clemarfolly/Microdigital-TK2000/EsquemaOriginal/tk2000.jpg

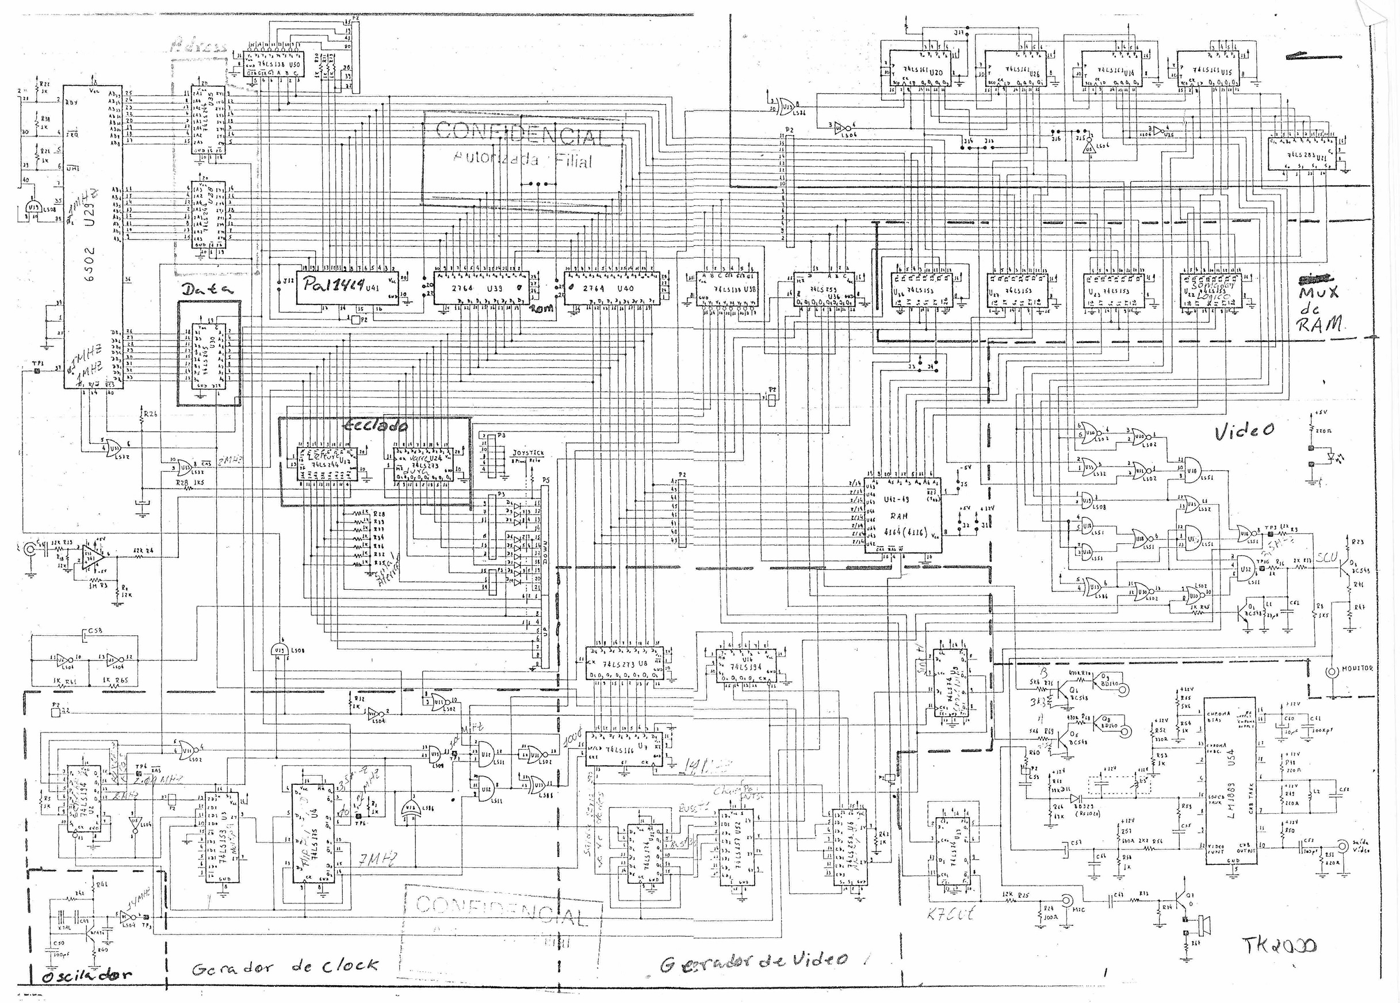
EsquemaOriginal/tk2000.jpg
