clemarfolly/Microdigital-TK2000/Fotos/Corrigido/tk2000_b.jpg

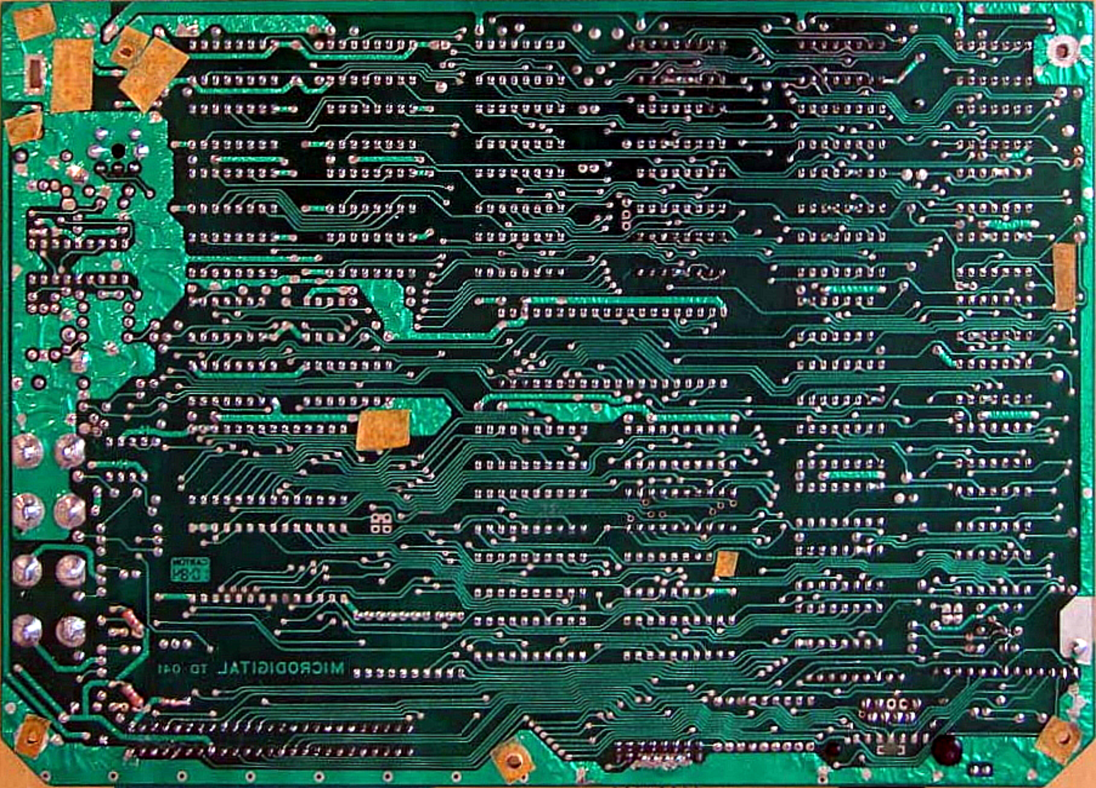
Fotos/Corrigido/tk2000_b.jpg
