clemarfolly/Microdigital-TK2000/Fotos/Corrigido/tk2000_pre_b.png

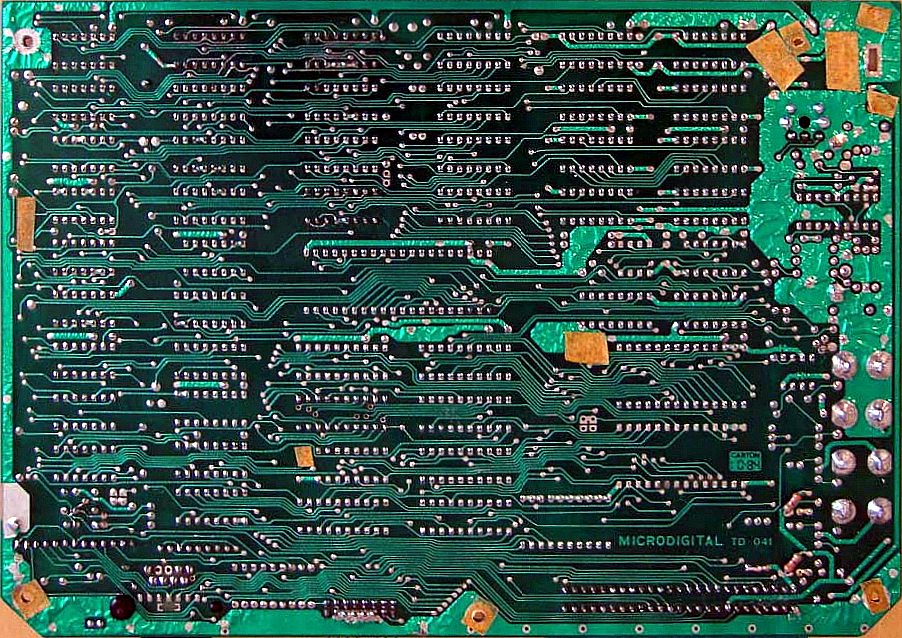
Fotos/Corrigido/tk2000_pre_b.png
