clemarfolly/Microdigital-TK2000/Fotos/Corrigido/tk2000_pre_f2.jpg

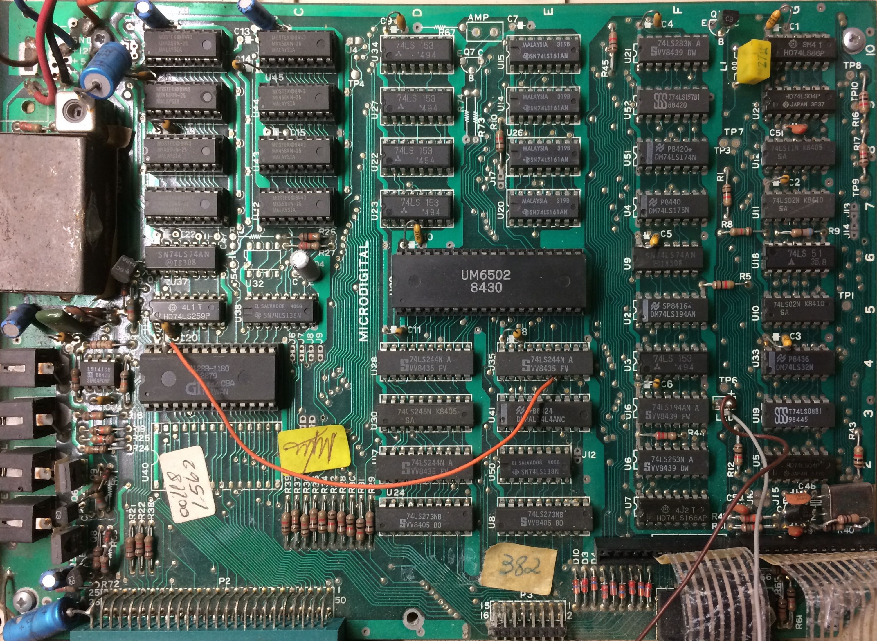
Fotos/Corrigido/tk2000_pre_f2.jpg
