clemarfolly/Microdigital-TK2000/Fotos/Corrigido/tk2000_pre_f.jpg

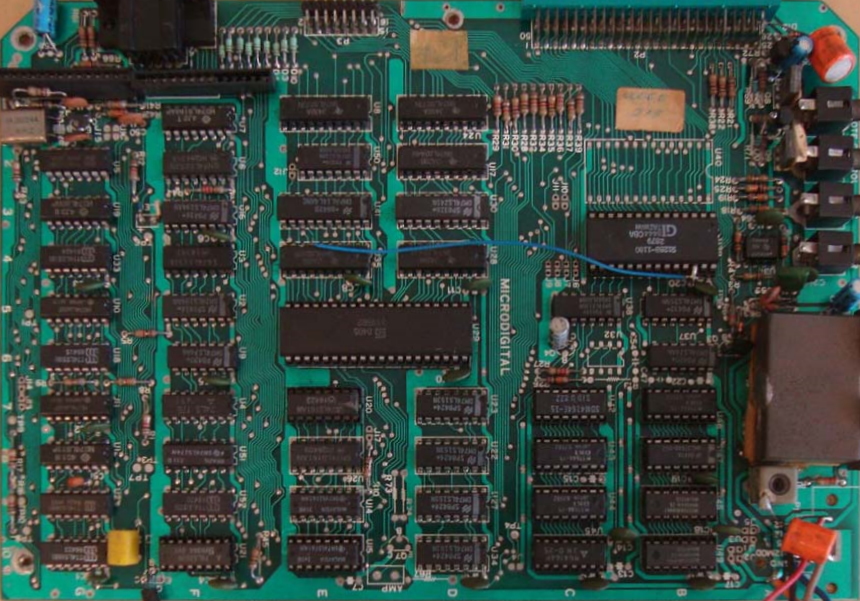
Fotos/Corrigido/tk2000_pre_f.jpg
