clemarfolly/Microdigital-TK2000/Fotos/Original/9.jpg

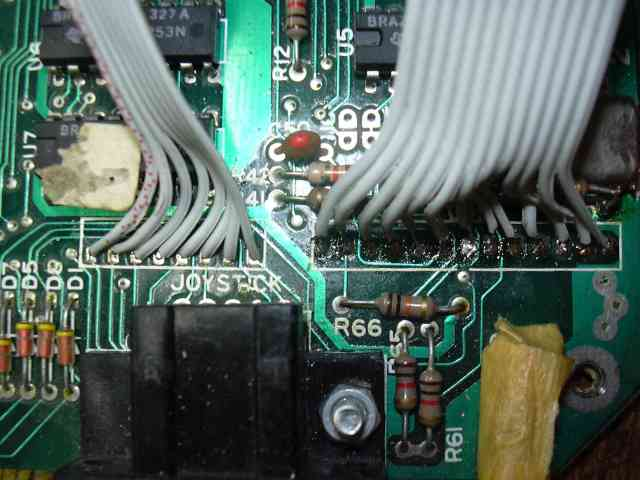
Fotos/Original/9.jpg
