clemarfolly/Microdigital-TK2000/Fotos/Original/117225193_1675733515915561_8471204110769268114_n.jpg

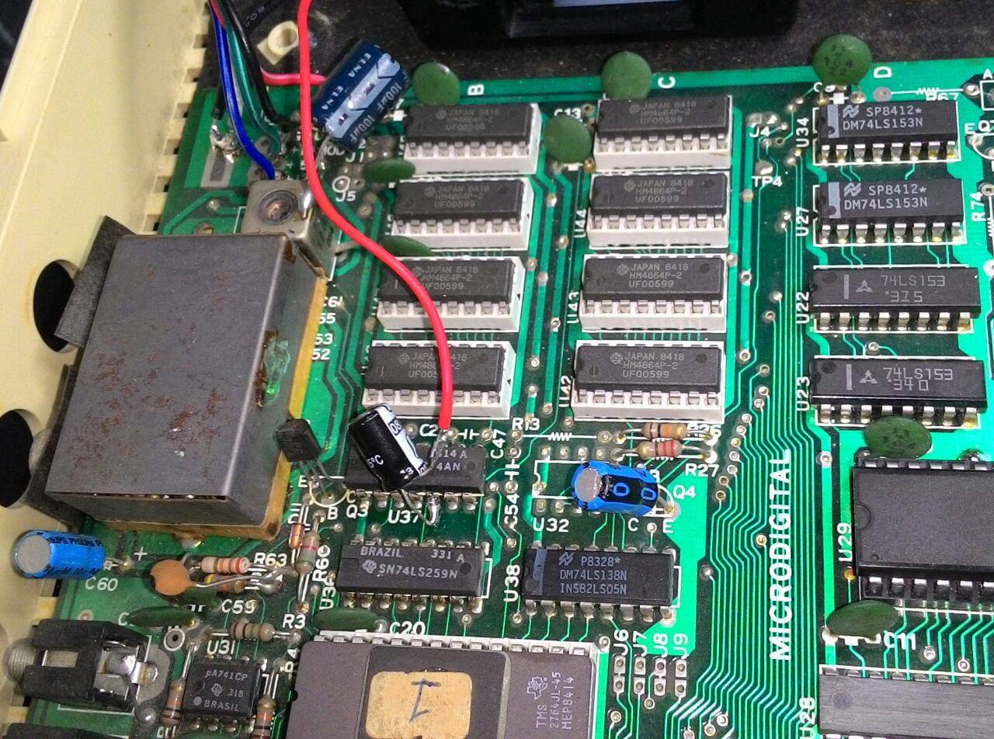
Fotos/Original/117225193_1675733515915561_8471204110769268114_n.jpg
