clemarfolly/Microdigital-TK2000/Fotos/Original/fotospcbtk20002/20221020_185743.jpg

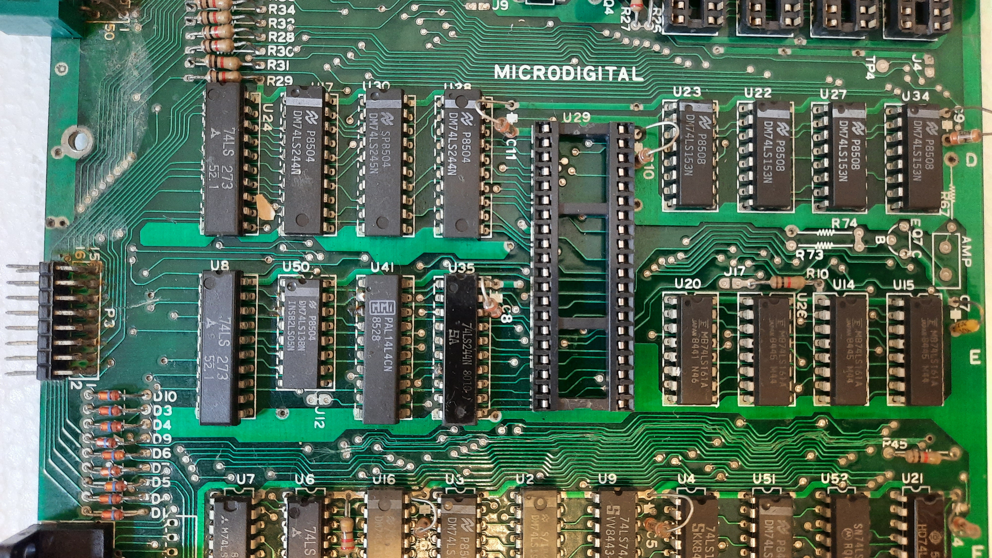
Fotos/Original/fotospcbtk20002/20221020_185743.jpg
