clemarfolly/Microdigital-TK2000/Fotos/Original/Multitech_MPF-II_02.jpg

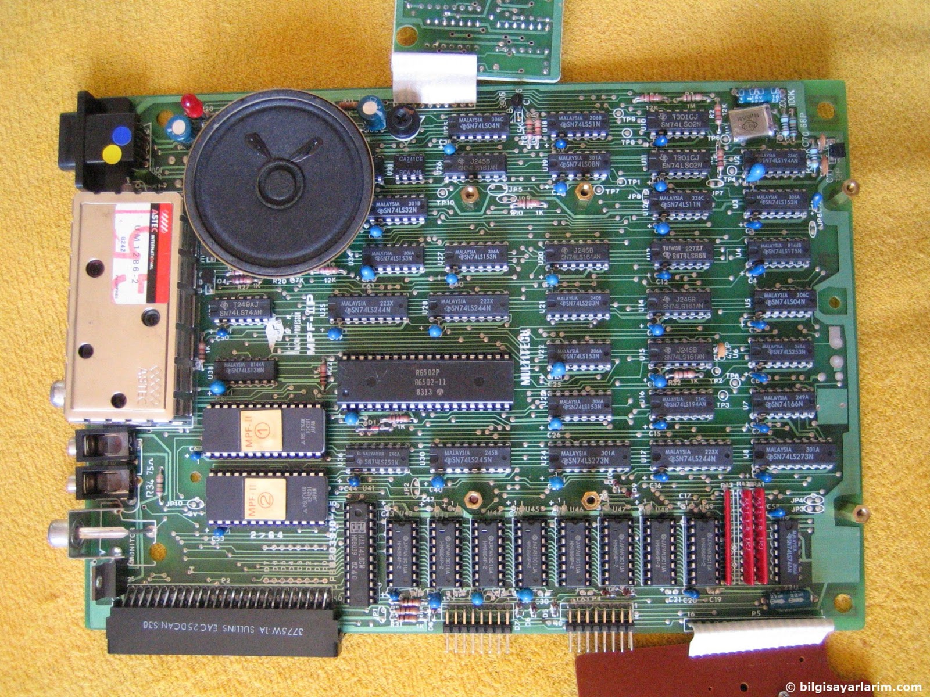
Fotos/Original/Multitech_MPF-II_02.jpg
