clemarfolly/Microdigital-TK2000/Fotos/Original/Projetos_TK2000_clareamento(9).jpg

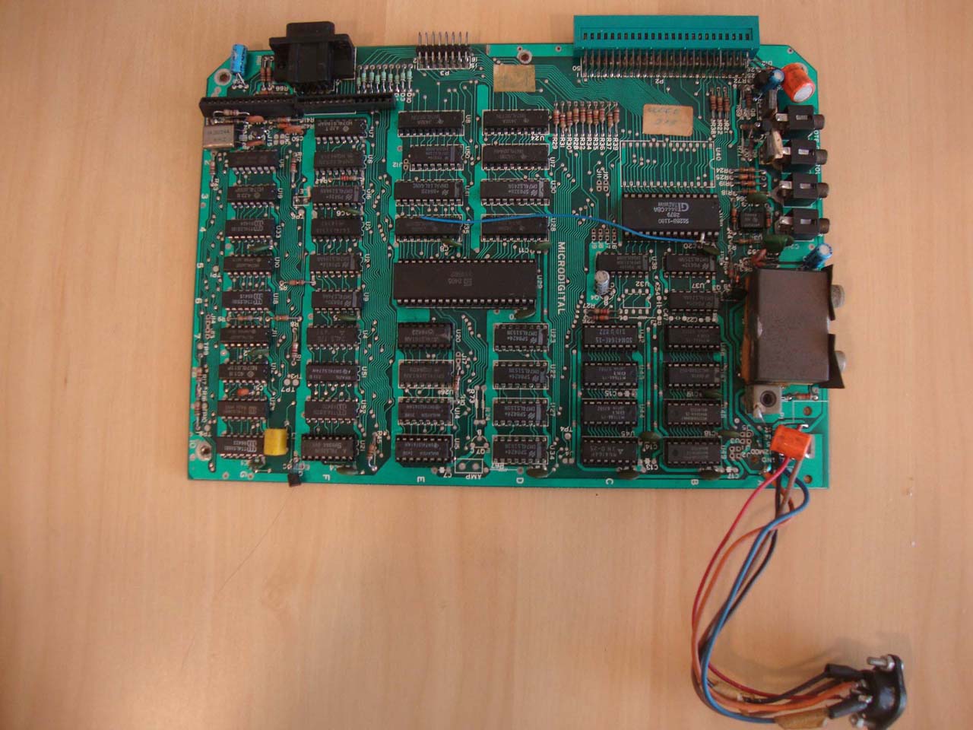
Fotos/Original/Projetos_TK2000_clareamento(9).jpg
