clemarfolly/Microdigital-TK2000/Fotos/Original/Projetos_TK2000_saida_som(3).jpg

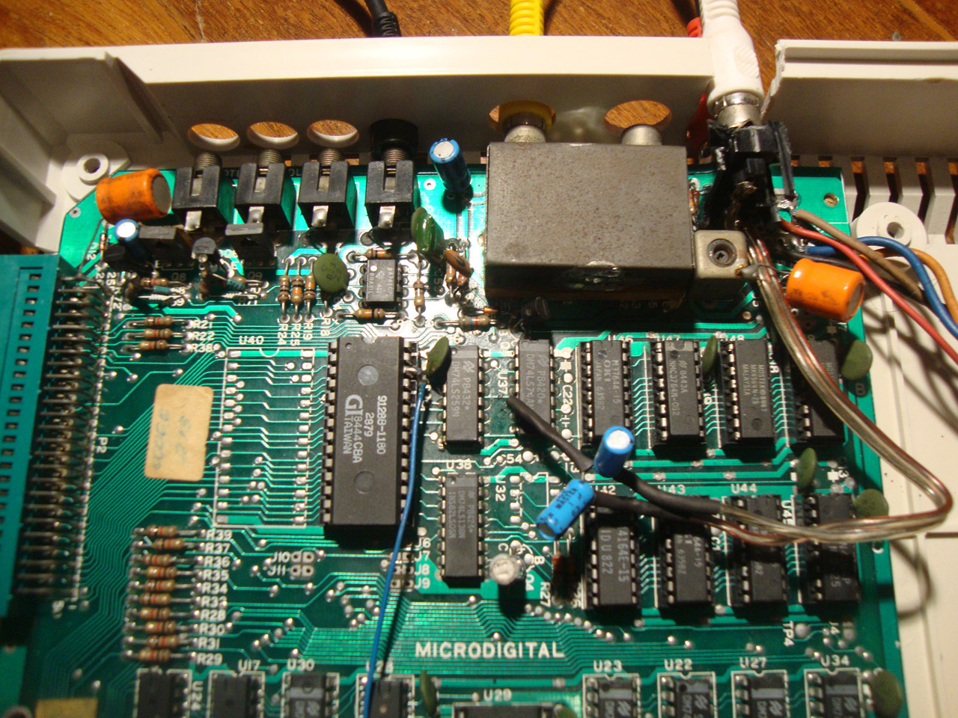
Fotos/Original/Projetos_TK2000_saida_som(3).jpg
