clemarfolly/Microdigital-TK2000/Fotos/Original/tk-2000 (5).jpg

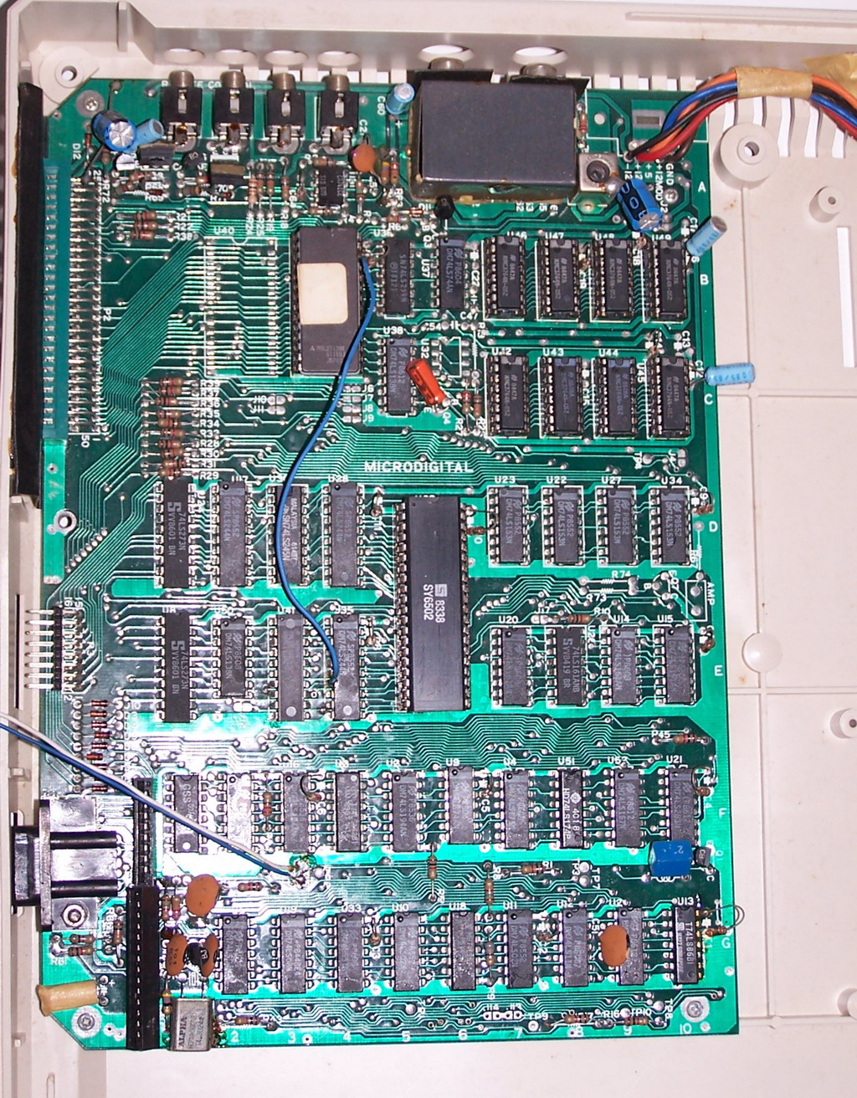
Fotos/Original/tk-2000 (5).jpg
