clemarfolly/Microdigital-TK2000/Imagens/tk2000.png

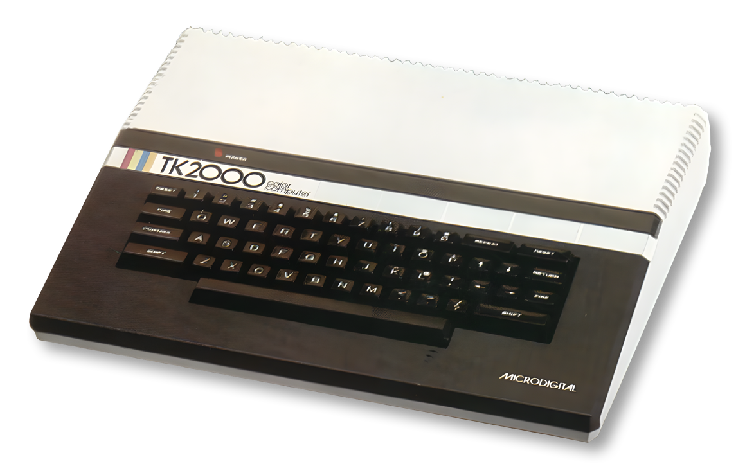
Imagens/tk2000.png
