clemarfolly/Microdigital-TK2000/Imagens/TK2000_b.png

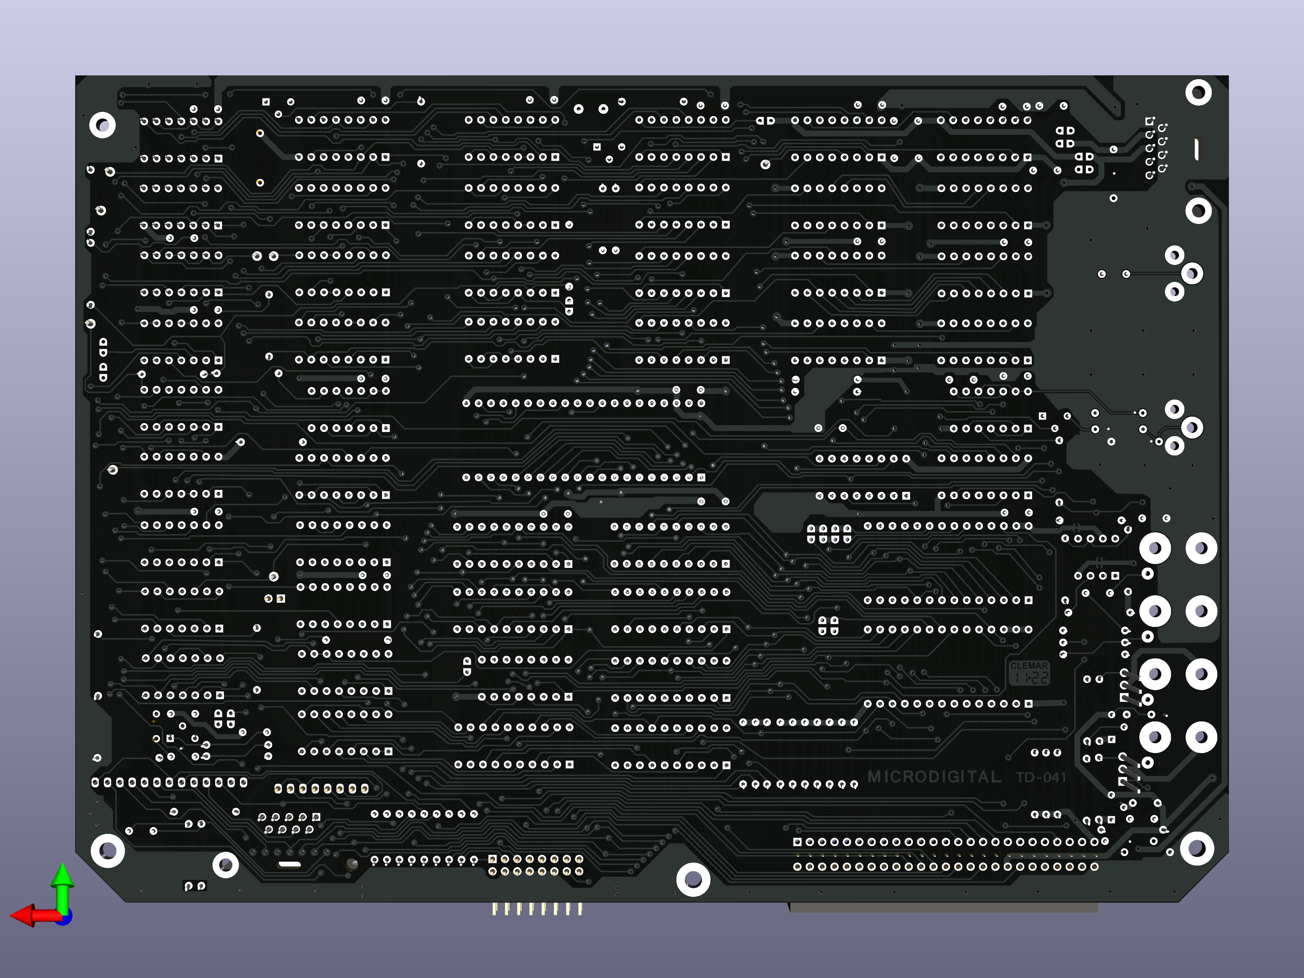
Imagens/TK2000_b.png
