clemarfolly/Microdigital-TK2000/Imagens/TK2000_b_comparacao.PNG

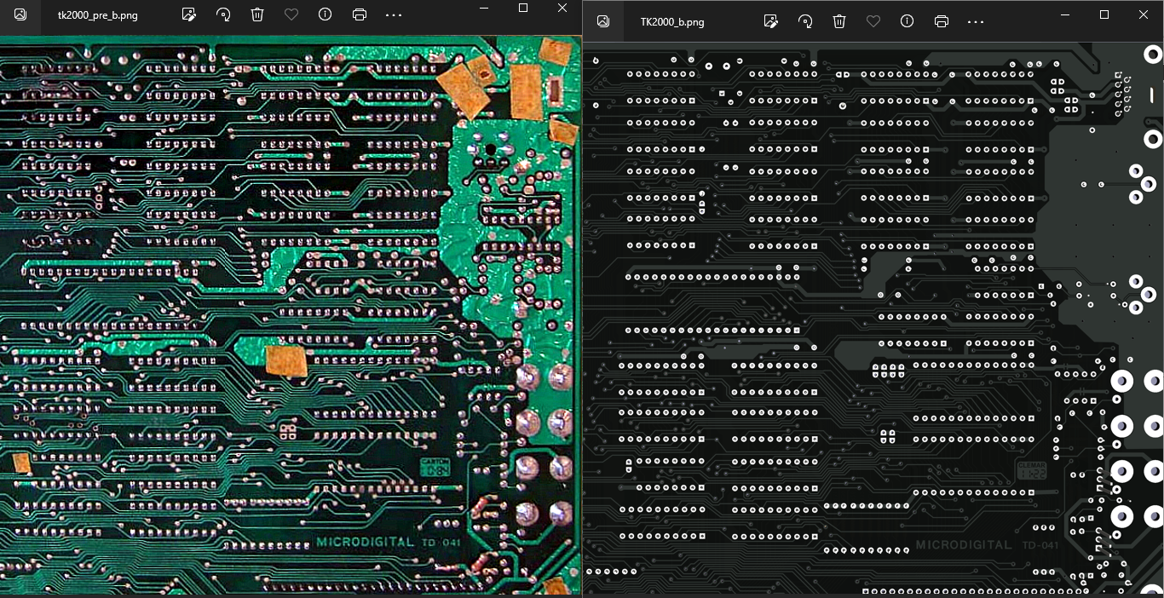
Imagens/TK2000_b_comparacao.PNG
