clemarfolly/Microdigital-TK2000/Imagens/TK2000_f_comparacao.PNG

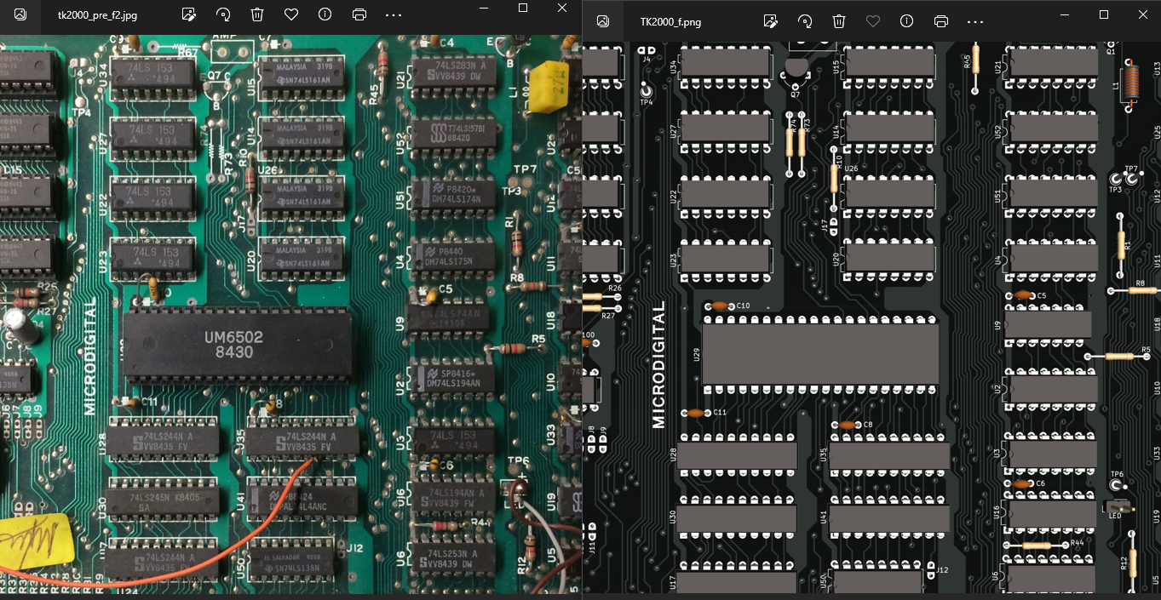
Imagens/TK2000_f_comparacao.PNG
