clemarfolly/Microdigital-TK2000/Imagens/tk2000_roteamento.png

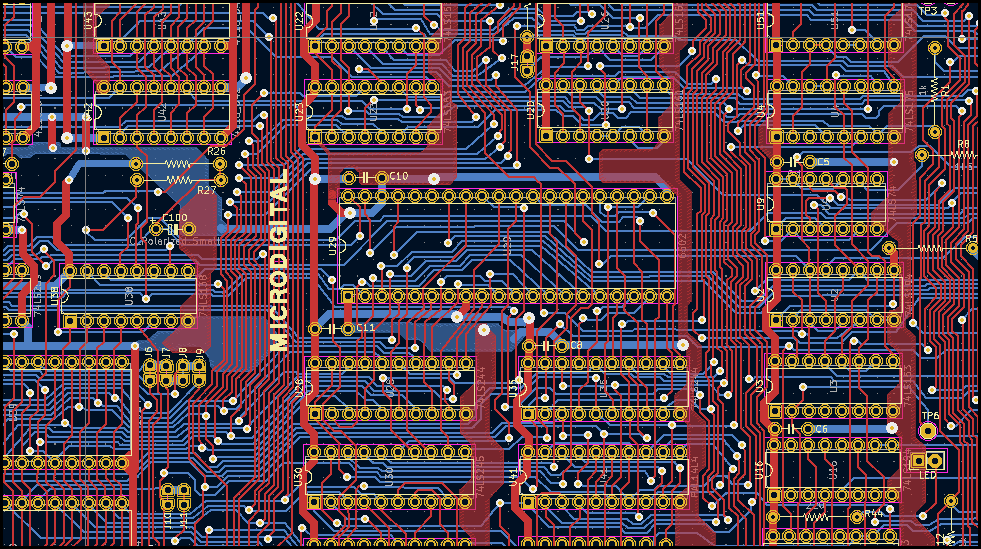
Imagens/tk2000_roteamento.png
