clemarfolly/Microdigital-TK2000/Interface de Drive/Fotos/placa_drive_lc_cheia.jpg

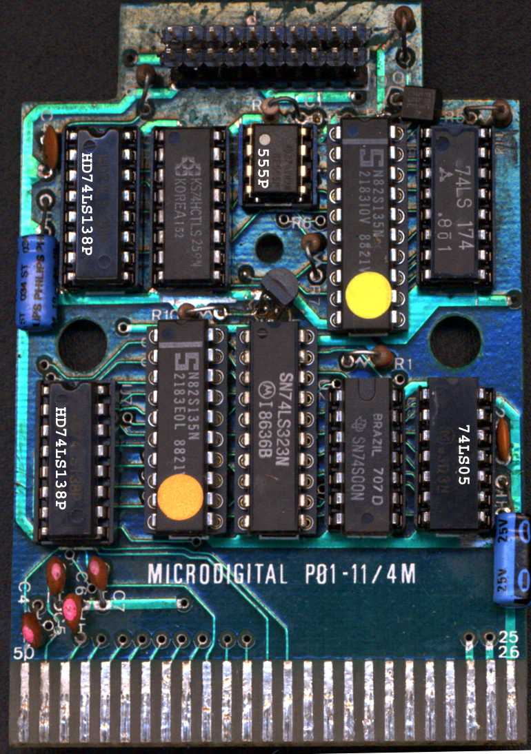
Interface de Drive/Fotos/placa_drive_lc_cheia.jpg
