clemarfolly/Microdigital-TK2000/Interface de Drive/Fotos/placa_drive_ls_cheia.jpg

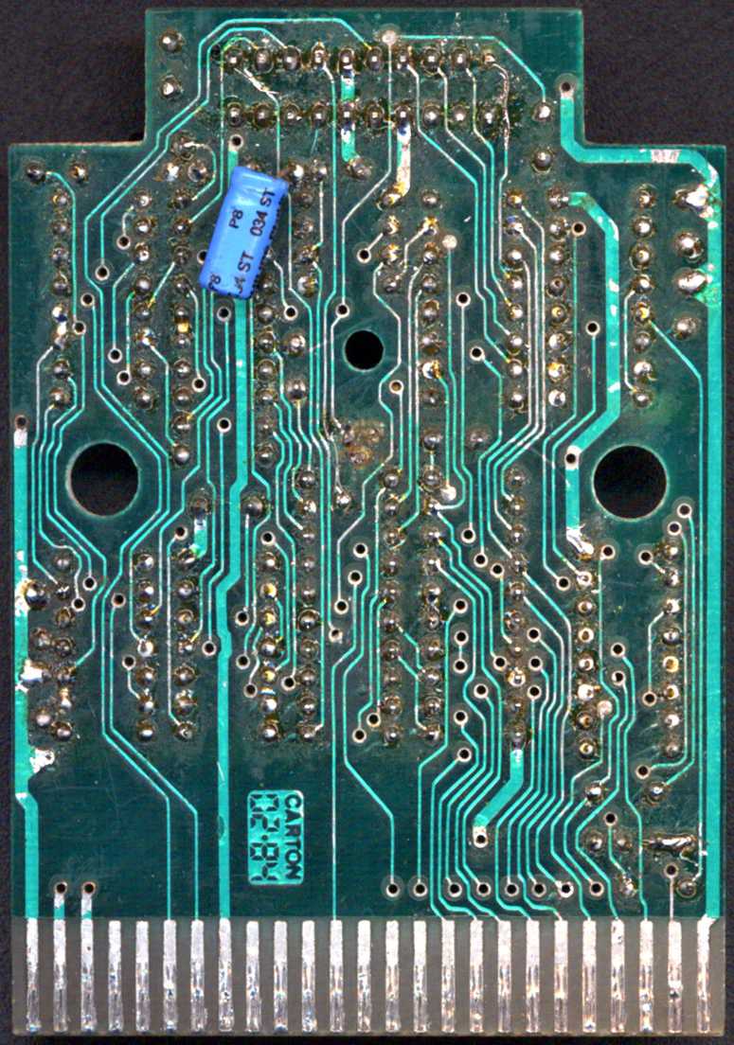
Interface de Drive/Fotos/placa_drive_ls_cheia.jpg
